liveboxandy/Gotek-Compatible-AT3F435-26Pin-SMD/MOD/SKRTLBE010.stp

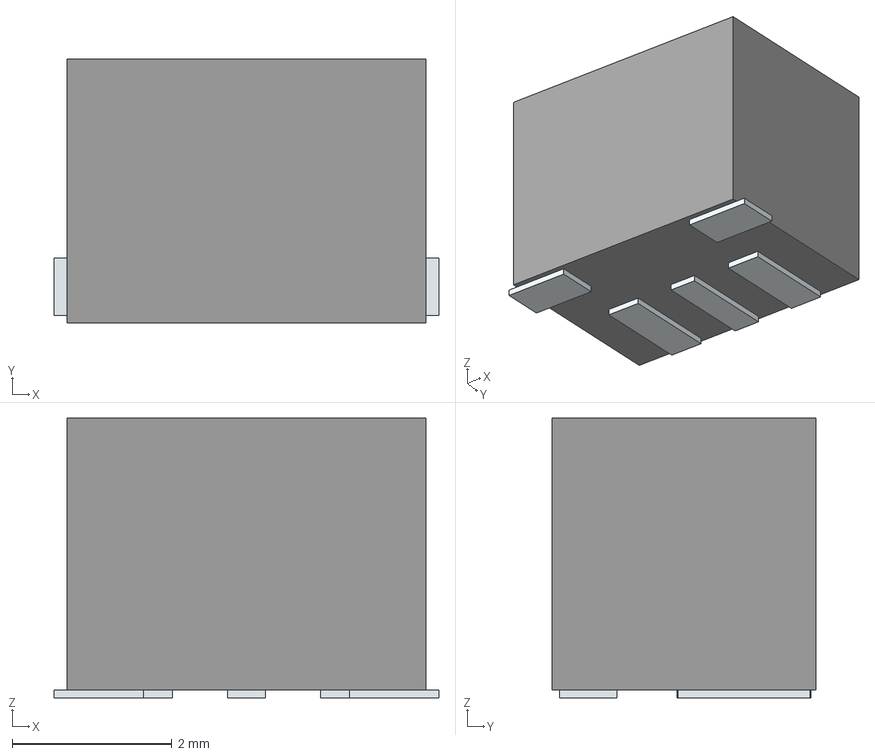
[picture p17: CAD file, 2025-03-06]
MOD/SKRTLBE010.stp
4.82 x 3.30 x 3.50 mm
Pins
