liveboxandy/Gotek-Compatible-AT3F435-26Pin-SMD/MOD/LFXTAL050985Bulk.stp

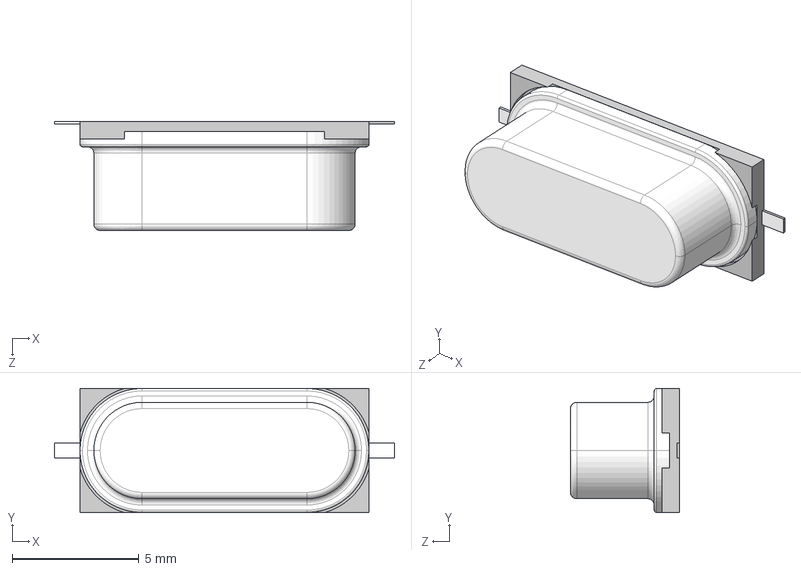
[picture p18: CAD file, 2025-03-06]
MOD/LFXTAL050985Bulk.stp
13.4 x 4.90 x 4.30 mm
