liveboxandy/Gotek-Compatible-AT3F435-26Pin-SMD/MOD/ABL-8.000MHZ-B2.stp

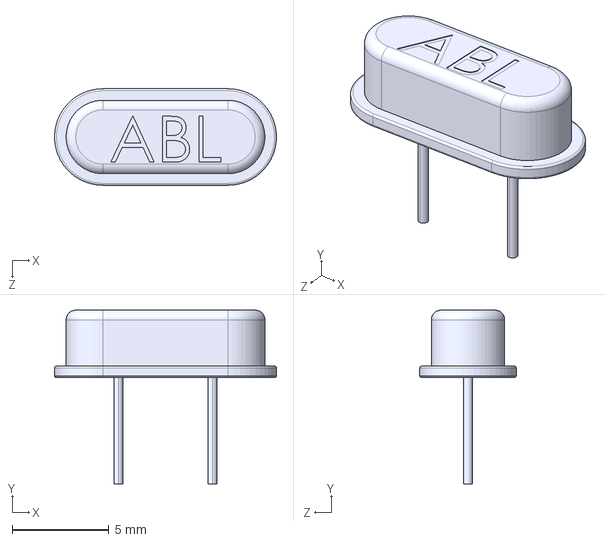
[picture p19: CAD file, 2025-03-06]
MOD/ABL-8.000MHZ-B2.stp
11.5 x 9.00 x 5.00 mm
