liveboxandy/Gotek-Compatible-AT3F435-26Pin-SMD/Gotek SMD.pdf

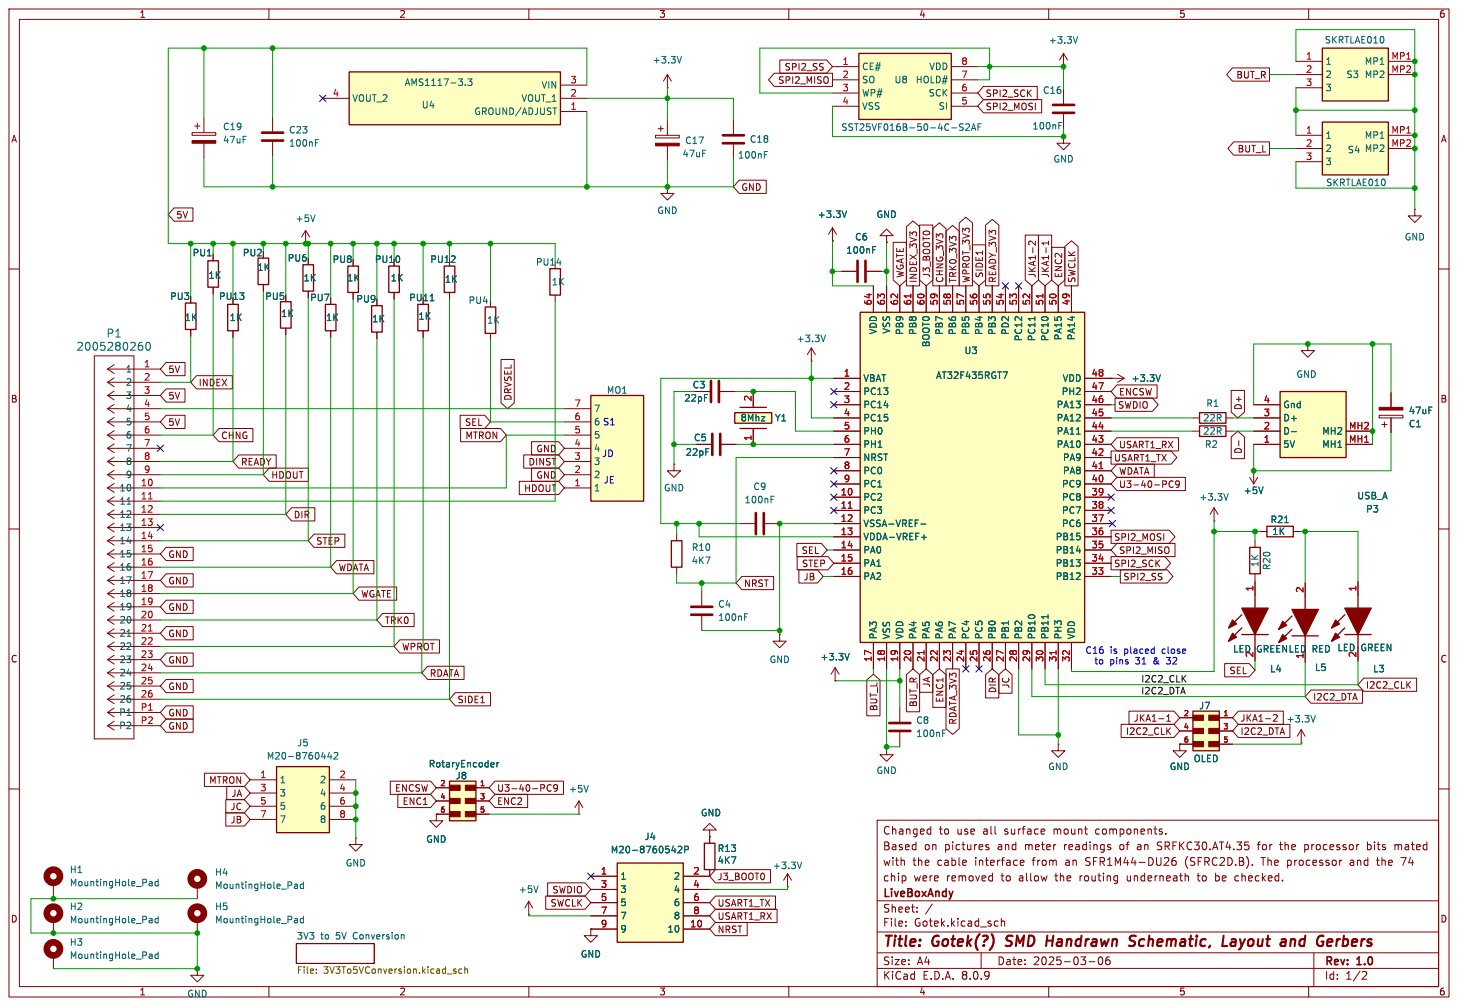
[picture p22: page 1]

File: Gotek.kicad_sch Sheet: / LiveBoxAndy

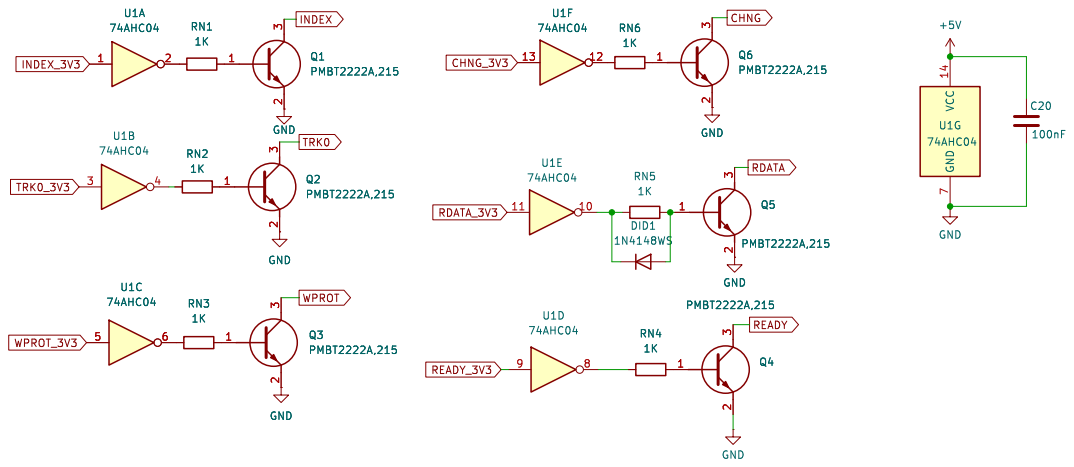
[picture p23: page 2]

File: 3V3To5VConversion.kicad_sch Sheet: /3V3 to 5V Conversion/ LiveBoxAndy
