liveboxandy/Gotek-Compatible-AT3F435-26Pin-SMD/Gotek TH.pdf

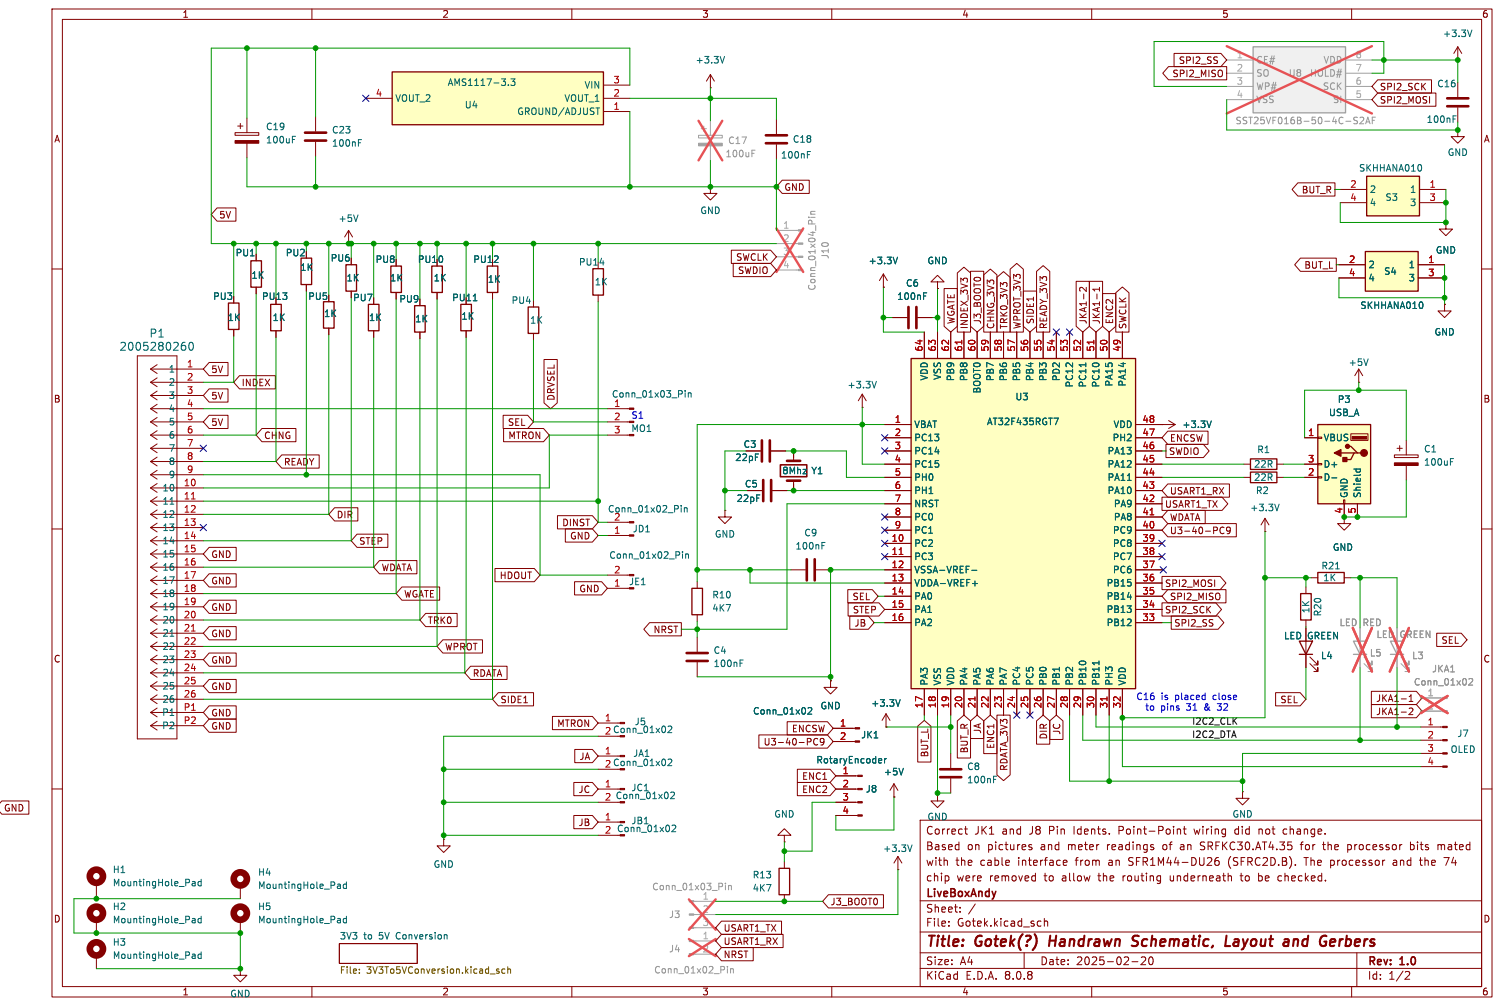
[picture p24: page 1]

STEP READY GND GND GND GND GND

File: Gotek.kicad_sch Sheet: / LiveBoxAndy


File: 3V3To5VConversion.kicad_sch Sheet: /3V3 to 5V Conversion/ LiveBoxAndy
